sh1319/IBM-AI-Watson-Pet-Project/CAD/Model1/touch sensor.SLDPRT

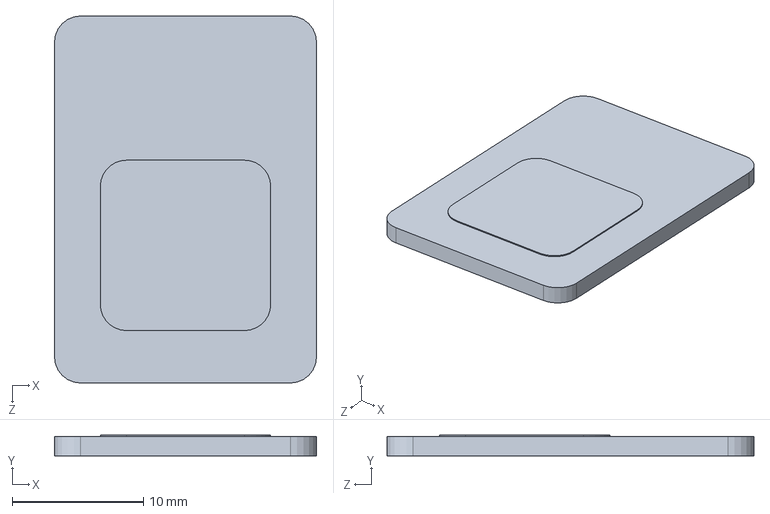
[picture p18: CAD file, 2022-09-01]
CAD/Model1/touch sensor.SLDPRT
20.0 x 1.60 x 28.0 mm
