sh1319/IBM-AI-Watson-Pet-Project/CAD/Model1/head spring.SLDPRT

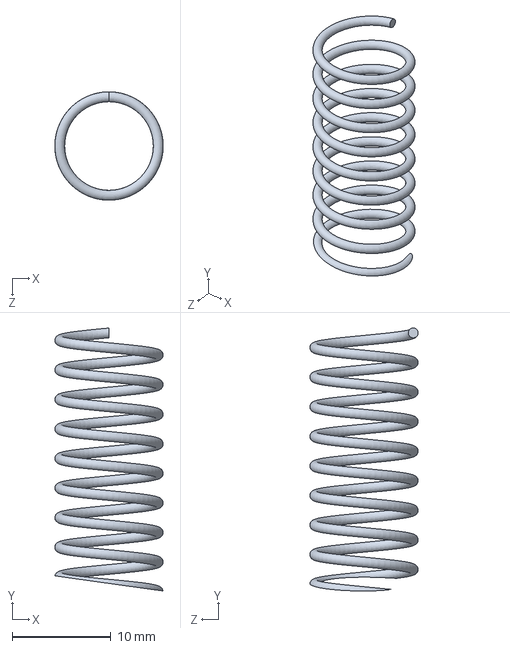
[picture p19: CAD file, 2022-09-01]
CAD/Model1/head spring.SLDPRT
11.0 x 26.7 x 11.0 mm
