sh1319/IBM-AI-Watson-Pet-Project/CAD/Model1/optional foot.SLDPRT

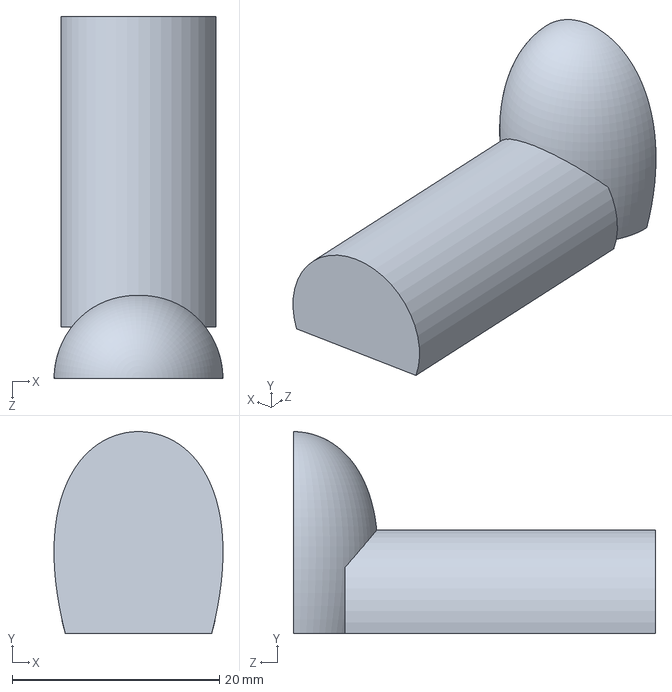
[picture p20: CAD file, 2022-09-01]
CAD/Model1/optional foot.SLDPRT
16.3 x 19.5 x 35.0 mm
